Arockiyalipson/Rapid-CoreX/Images/6 pin_ male_ header.jpg

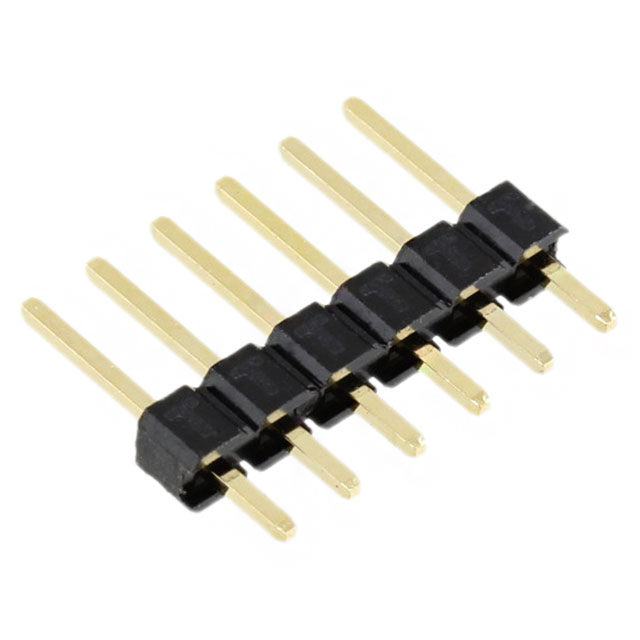
Images/6 pin_ male_ header.jpg
