Arockiyalipson/Rapid-CoreX/Images/PTS636SK25FSMTR LFS_SW1.jpg

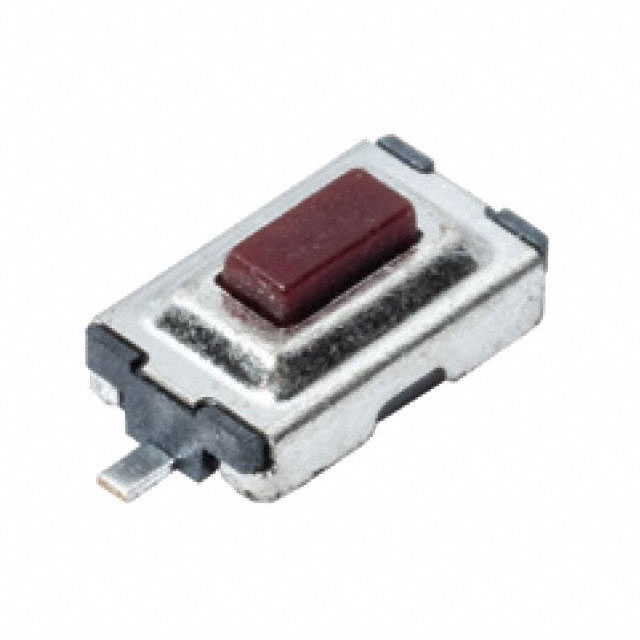
Images/PTS636SK25FSMTR LFS_SW1.jpg
