Arockiyalipson/Rapid-CoreX/Reference/Rapid_Core-X.jpg

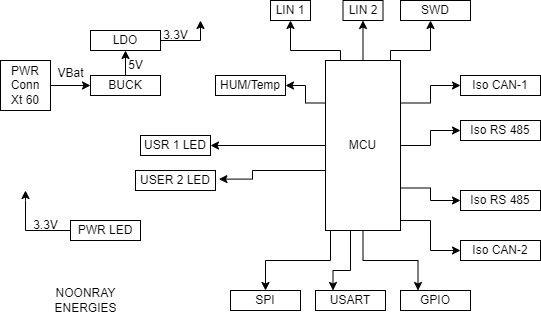
Reference/Rapid_Core-X.jpg
